analoghifi/Thel-AccuSound-100/docs/3) version 1995-2003/power_output_table_version_1995-2003__V2.jpg

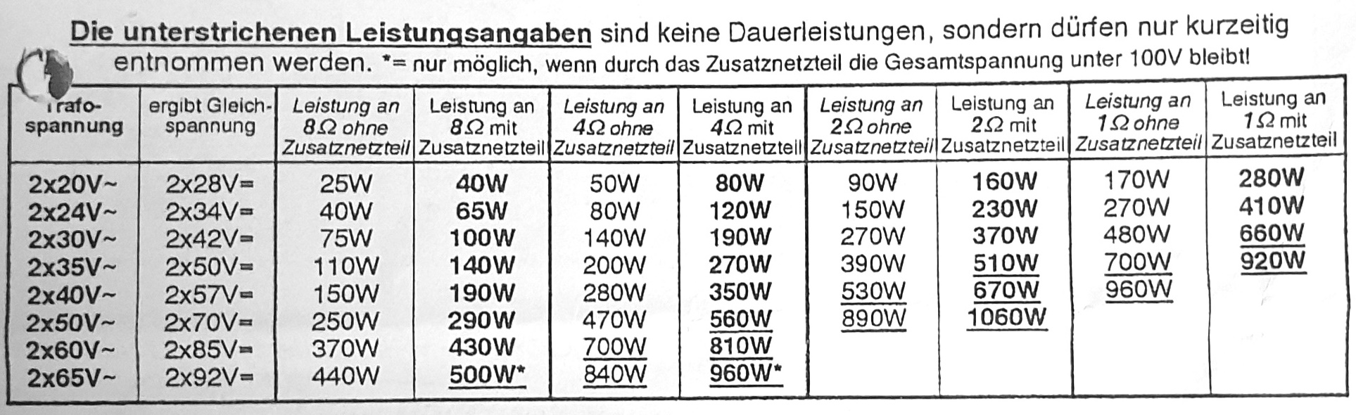
docs/3) version 1995-2003/power_output_table_version_1995-2003__V2.jpg
