analoghifi/Thel-AccuSound-100/docs/3) version 1995-2003/power_table_2002.png

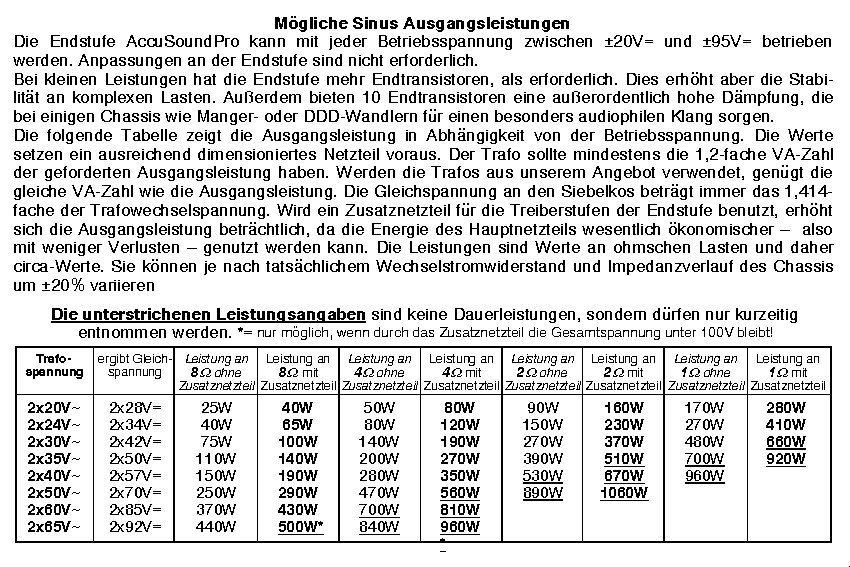
docs/3) version 1995-2003/power_table_2002.png
