analoghifi/Thel-AccuSound-100/docs/4.) final version 2003-2015/bridge_configuration.png

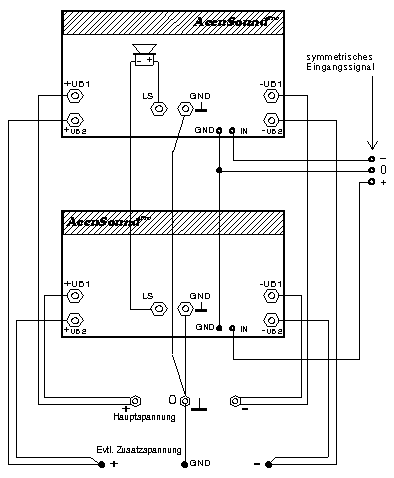
docs/4.) final version 2003-2015/bridge_configuration.png
