analoghifi/Thel-AccuSound-100/docs/4.) final version 2003-2015/CLASS-A.png

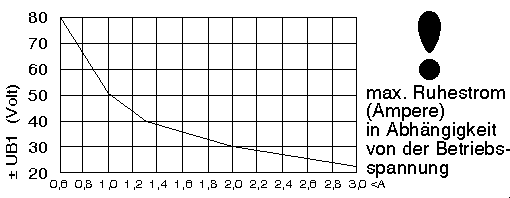
docs/4.) final version 2003-2015/CLASS-A.png
