analoghifi/Thel-AccuSound-100/docs/4.) final version 2003-2015/connection_plan_monoblock.png

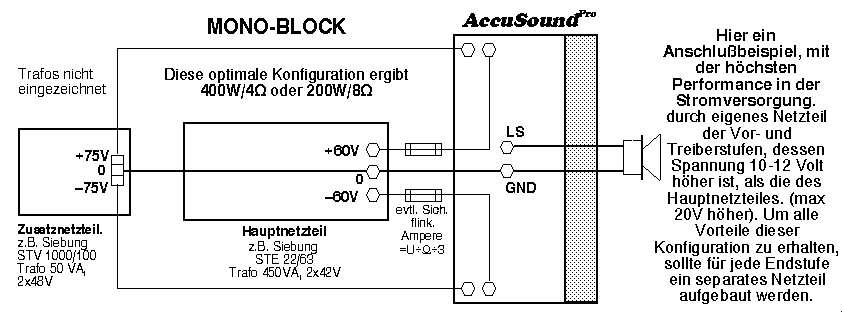
docs/4.) final version 2003-2015/connection_plan_monoblock.png
