analoghifi/Thel-AccuSound-100/docs/4.) final version 2003-2015/power_output_table_version_2003-2015.png

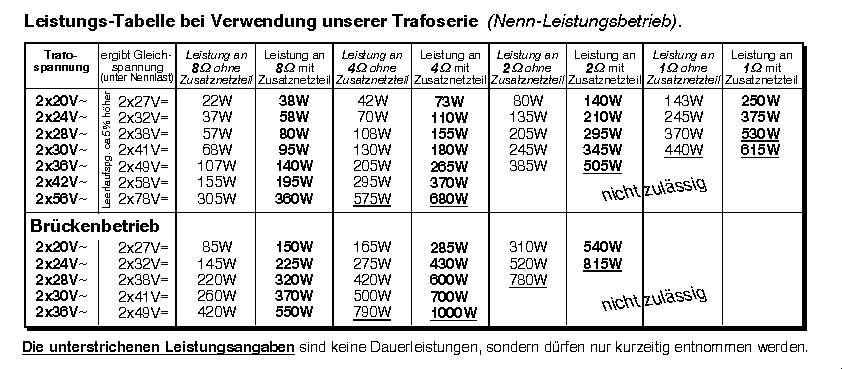
docs/4.) final version 2003-2015/power_output_table_version_2003-2015.png
