analoghifi/Thel-AccuSound-100/hardware/1) version ProAmp 1993/Thel_Proamp_1993.jpg

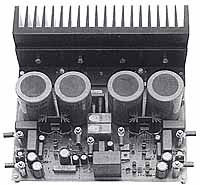
hardware/1) version ProAmp 1993/Thel_Proamp_1993.jpg
