analoghifi/Thel-AccuSound-100/hardware/2) version 1994/accusound_1994.jpg

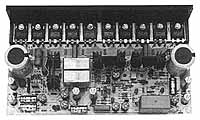
hardware/2) version 1994/accusound_1994.jpg
