analoghifi/Thel-AccuSound-100/hardware/3) version 1995-2003/accousound_100_3.jpg

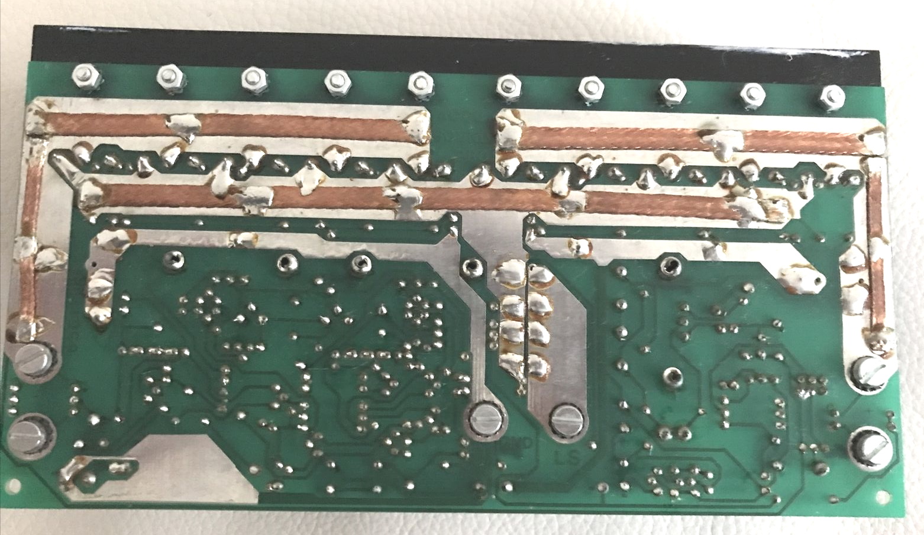
hardware/3) version 1995-2003/accousound_100_3.jpg
