analoghifi/Thel-AccuSound-100/hardware/3) version 1995-2003/accousound_100_7.jpg

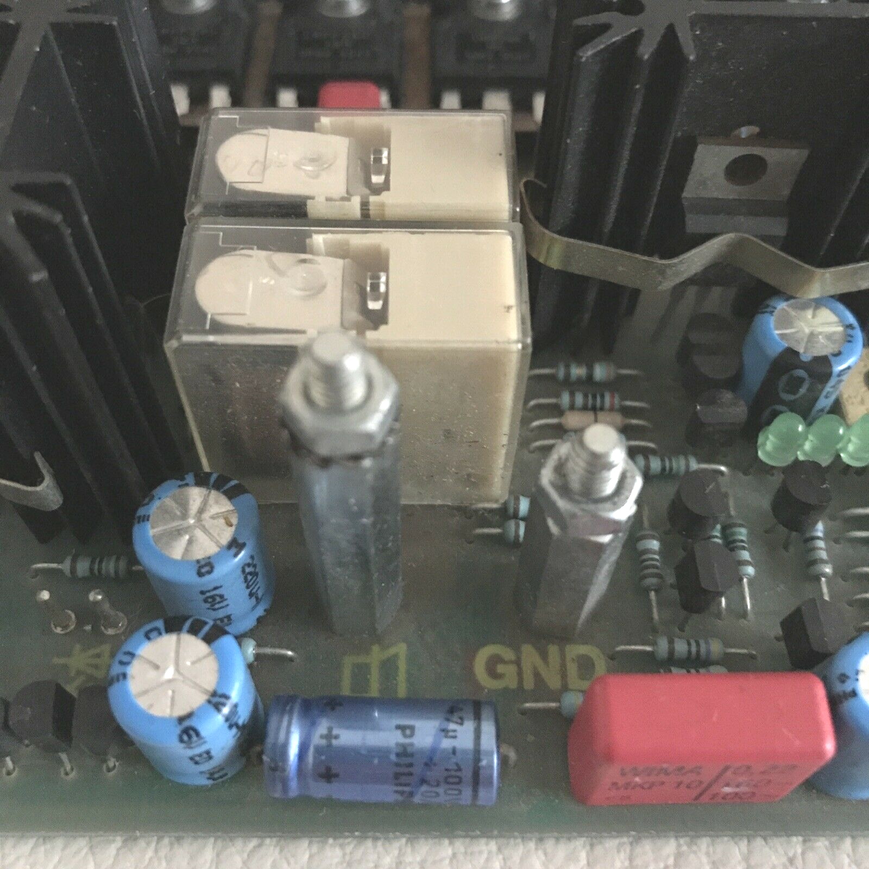
hardware/3) version 1995-2003/accousound_100_7.jpg
