analoghifi/Thel-AccuSound-100/hardware/3) version 1995-2003/accusound_2002.jpg

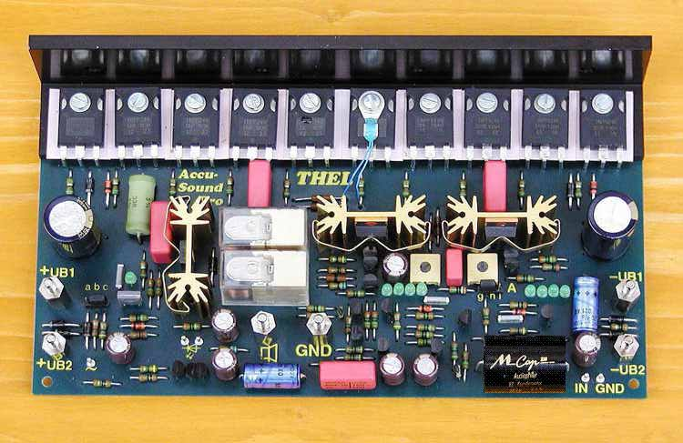
hardware/3) version 1995-2003/accusound_2002.jpg
