analoghifi/Thel-AccuSound-100/hardware/3) version 1995-2003/AccuSound_pro_101.jpg

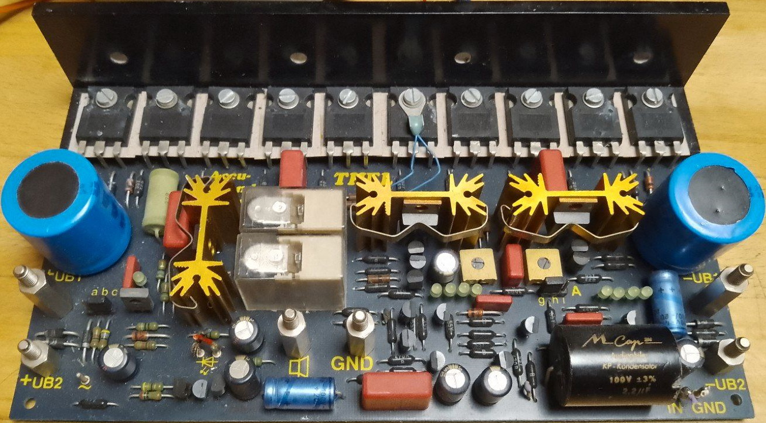
hardware/3) version 1995-2003/AccuSound_pro_101.jpg
