analoghifi/Thel-AccuSound-100/hardware/3) version 1995-2003/accusound_pro_1995-2003.jpg

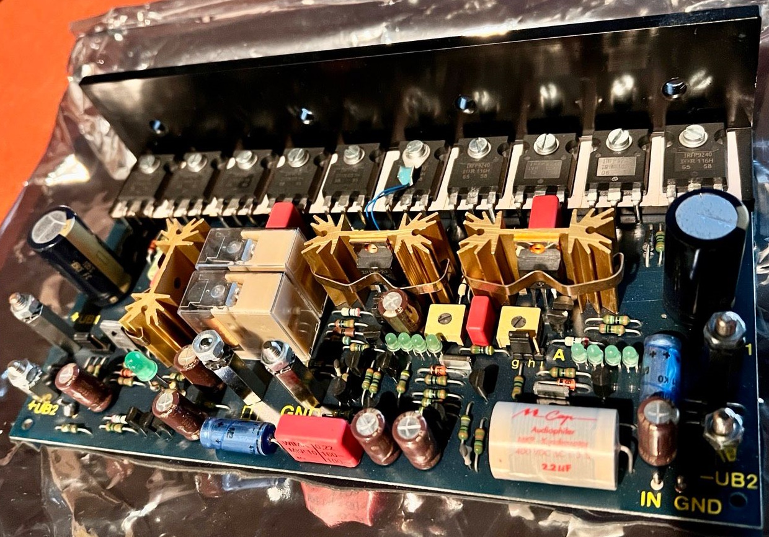
hardware/3) version 1995-2003/accusound_pro_1995-2003.jpg
