analoghifi/Thel-AccuSound-100/hardware/3) version 1995-2003/accusound_version_1995-2003_schematic_V2.jpg

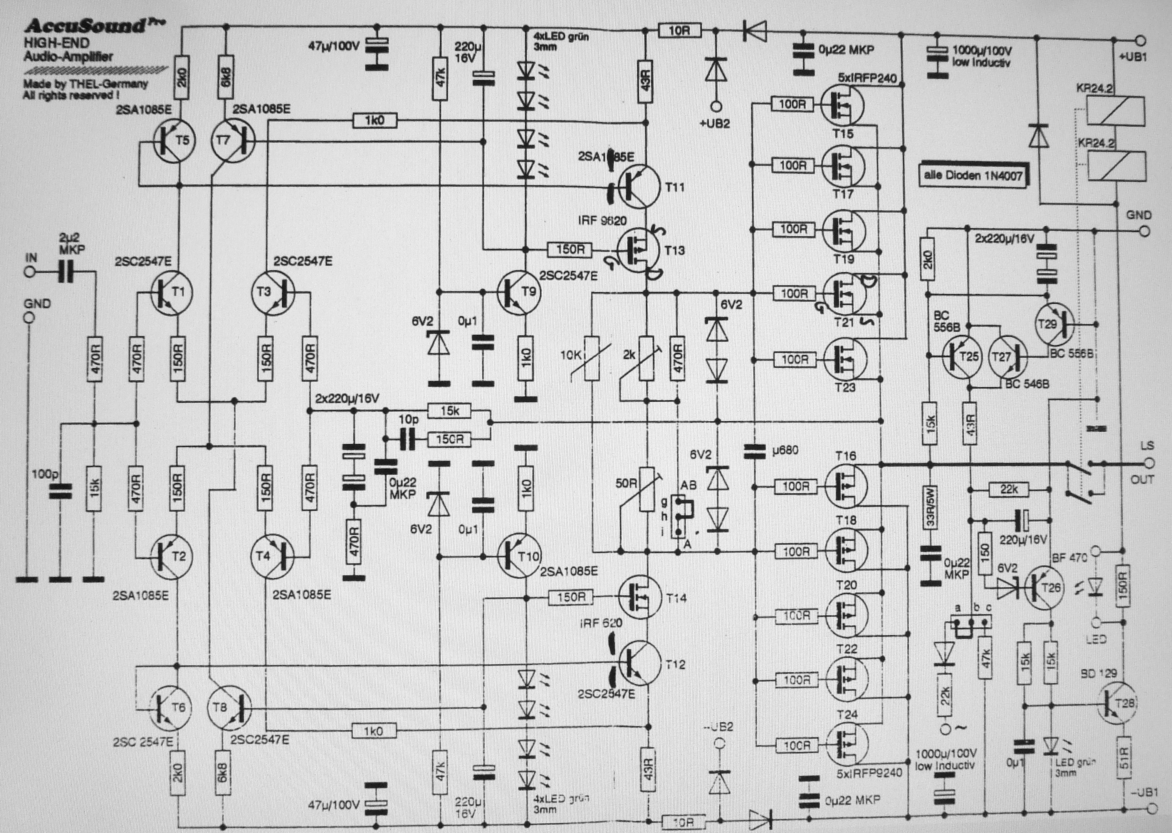
hardware/3) version 1995-2003/accusound_version_1995-2003_schematic_V2.jpg
