analoghifi/Thel-AccuSound-100/hardware/4.) final version 2003-2015/4.1) version 2003-2006/accuSound_100__2003-2006.jpg

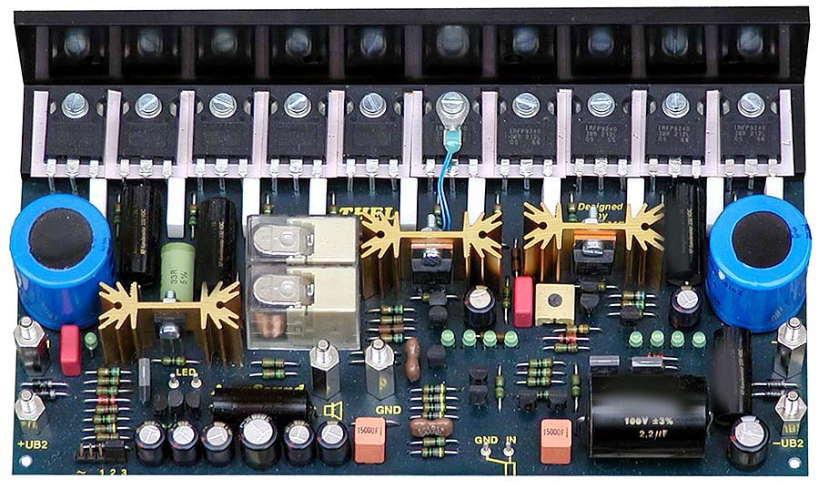
hardware/4.) final version 2003-2015/4.1) version 2003-2006/accuSound_100__2003-2006.jpg
