analoghifi/Thel-AccuSound-100/hardware/4.) final version 2003-2015/4.2) version 2006-2011/accuSound_100__2006-2011_backside.jpg

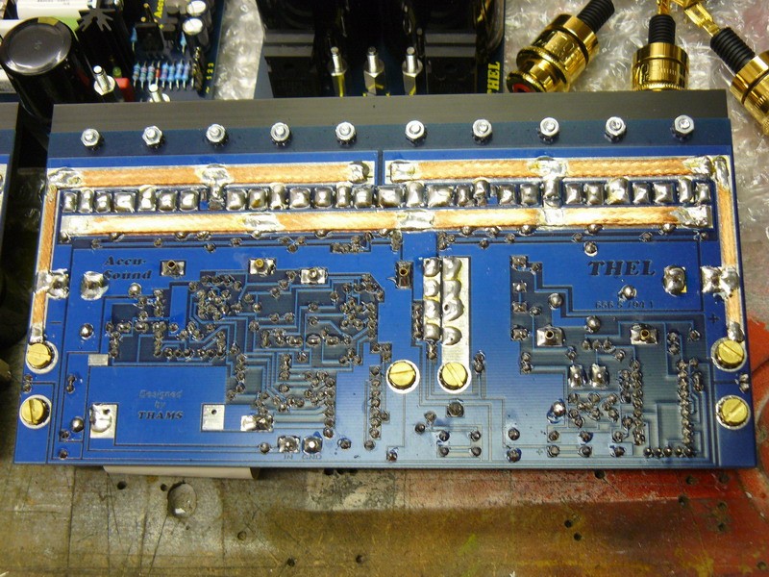
hardware/4.) final version 2003-2015/4.2) version 2006-2011/accuSound_100__2006-2011_backside.jpg
