analoghifi/Thel-AccuSound-100/hardware/4.) final version 2003-2015/4.2) version 2006-2011/detail-photos/perspective-top-details/AccuSound_101__2006-2011__top_detail_5.jpg

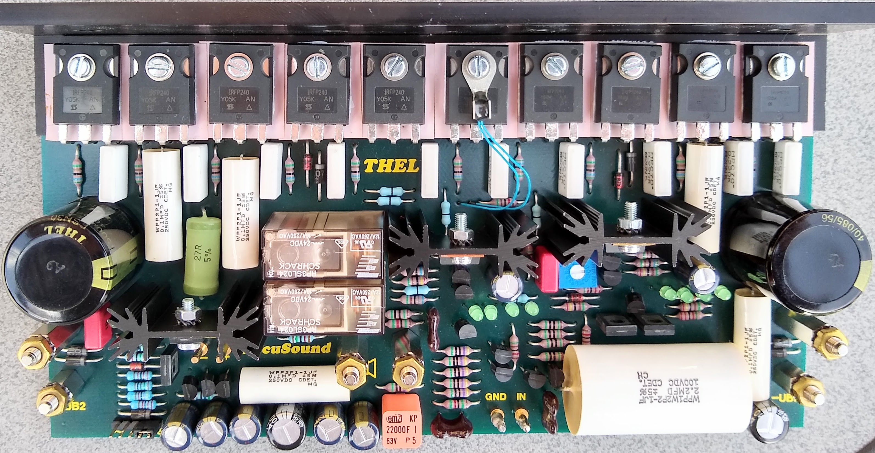
hardware/4.) final version 2003-2015/4.2) version 2006-2011/detail-photos/perspective-top-details/AccuSound_101__2006-2011__top_detail_5.jpg
