analoghifi/Thel-AccuSound-100/hardware/4.) final version 2003-2015/4.2) version 2006-2011/KiCad/original/AccuSound100_2006-2011_orig_1layer_THT__top.png

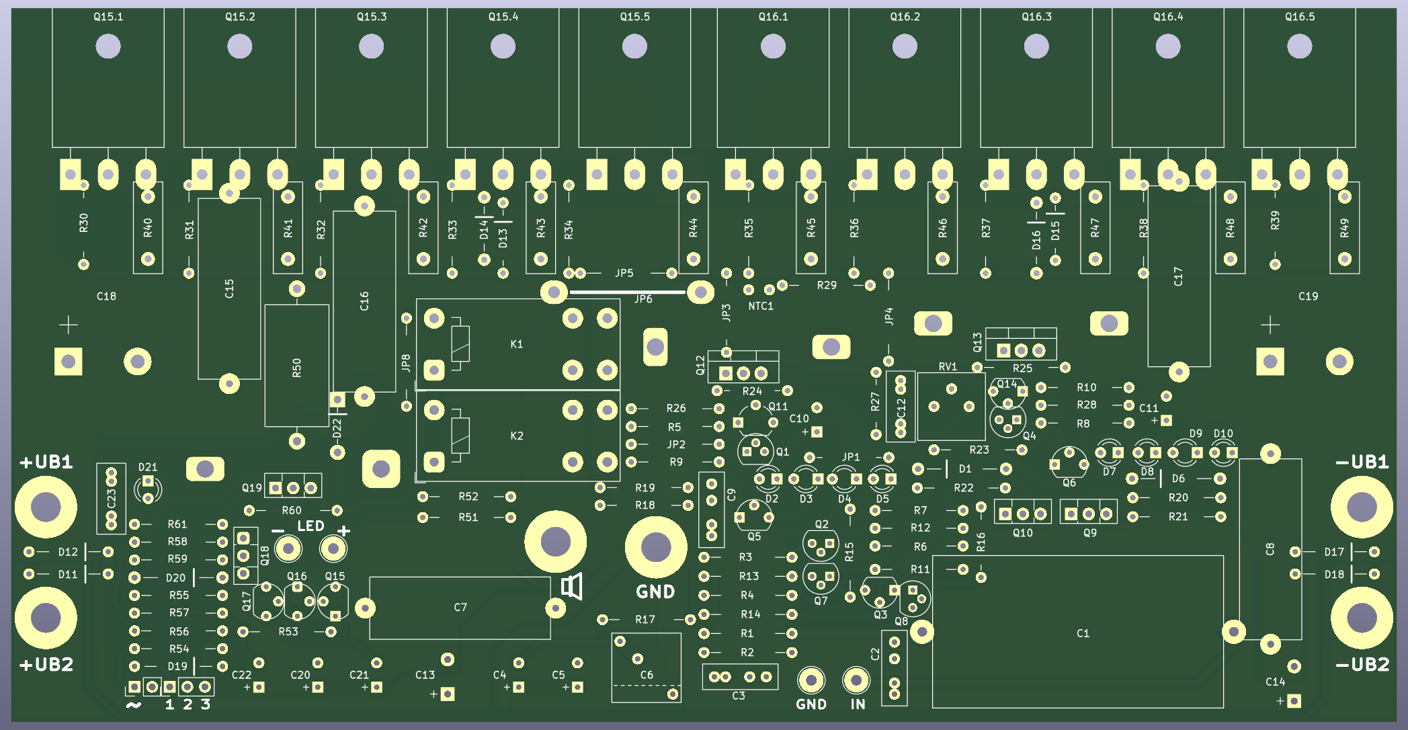
hardware/4.) final version 2003-2015/4.2) version 2006-2011/KiCad/original/AccuSound100_2006-2011_orig_1layer_THT__top.png
