analoghifi/Thel-AccuSound-100/hardware/4.) final version 2003-2015/4.3) version 2011-2015/accuSound_100__2011-2015__3.jpg

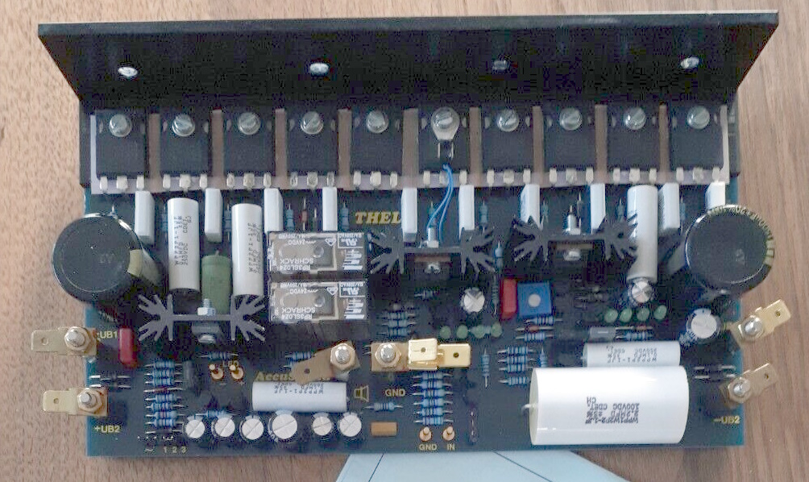
hardware/4.) final version 2003-2015/4.3) version 2011-2015/accuSound_100__2011-2015__3.jpg
