analoghifi/Thel-AccuSound-100/hardware/4.) final version 2003-2015/AccuSound_100_schematic_2004__corrected.jpg

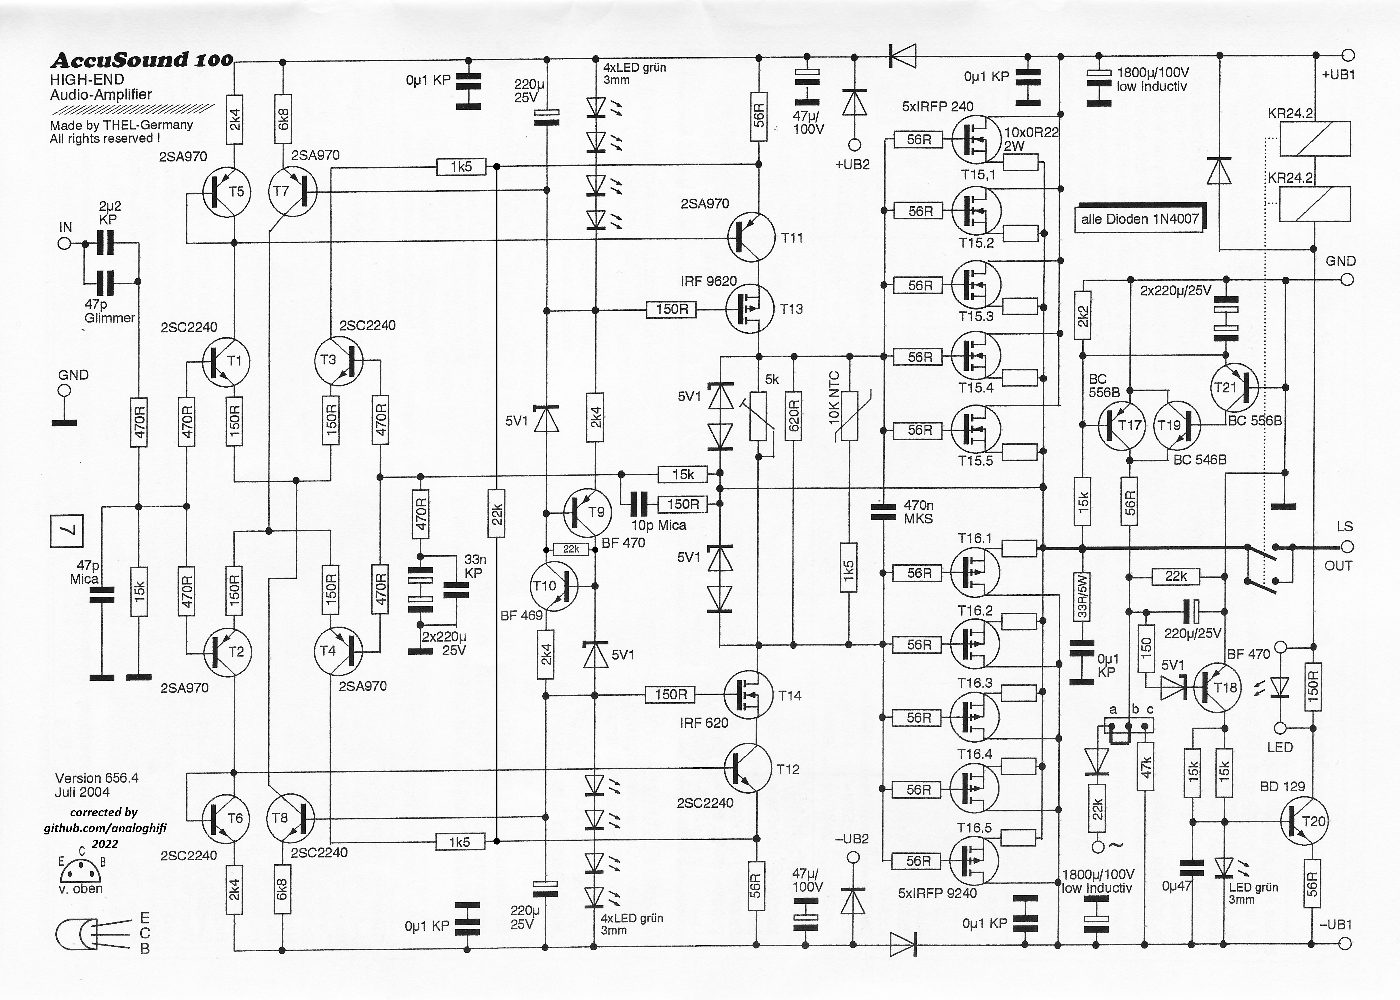
hardware/4.) final version 2003-2015/AccuSound_100_schematic_2004__corrected.jpg
