analoghifi/Thel-AccuSound-100/hardware/4.) final version 2003-2015/compare_accousound_versions_4.2)_vs_4.3).jpg

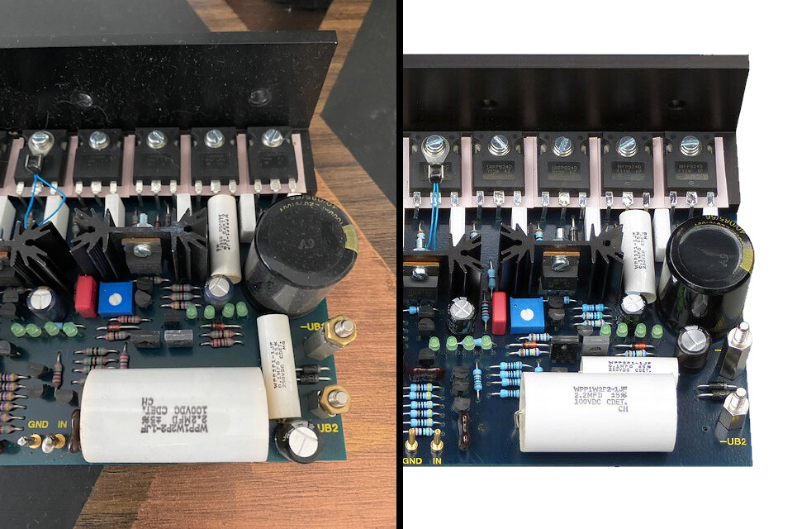
hardware/4.) final version 2003-2015/compare_accousound_versions_4.2)_vs_4.3).jpg
