analoghifi/Thel-AccuSound-100/docs/components datasheets/special relay version 1995-2003/Alternative: Weidmueller RCLS3T024(W)/Weidmueller_RCLS3T024(W)/Wiring_Diagram.jpg

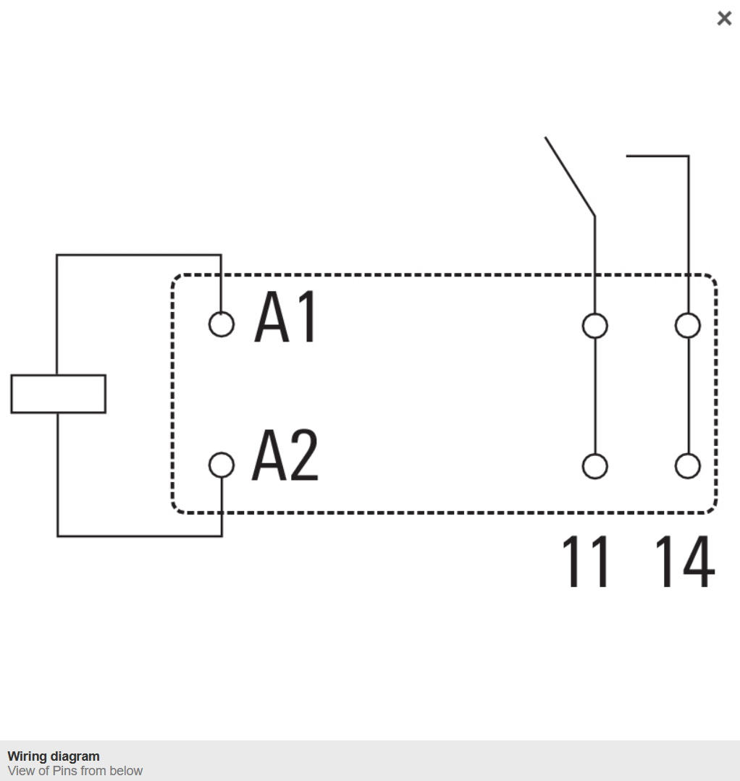
docs/components datasheets/special relay version 1995-2003/Alternative: Weidmueller RCLS3T024(W)/Weidmueller_RCLS3T024(W)/Wiring_Diagram.jpg
